opmedia-dev/k6_gpo_exhibit/firmware/src/phone_controller.h

#pragma once

#include <Arduino.h>
#include "config.h"
#include "phone_line.h"
#include "rotary_decoder.h"
#include "bell_driver.h"
#include "audio_player.h"
#include "control_panel.h"
#include "coin_box.h"

// ============================================================================
// Phone controller — exhibit state machine
//
// States:
//   IDLE             On-hook.  Auto-ring timer ticking.
//   RINGING          Bell ringing (auto or manual).  Awaiting pickup.
//   PLAYING_HISTORY  Handset answered a ring → playing a history track.
//   DIAL_TONE        Handset lifted without ring → dial tone plays.
//   DIALING          Digits accumulating from rotary dial.
//   AWAIT_COINS      (A+B only) Number recognised, waiting for coins.
//   AWAIT_BTN_A      (A+B only) Call connected, waiting for Button A.
//   AWAIT_BTN_B      (A+B only) Number not recognised, waiting for Button B.
//   RINGING_TONE    Outgoing call → playing UK ringing tone before connecting.
//   PLAYING_NUMBER   Dialling complete → matched MP3 playing.
//   PLAYING_NOT_REC  Dialling complete → "number not recognised" playing.
//   BUSY             Error / timeout → busy tone.
//   PLUGIN_SEQUENCE  Executing a JSON plugin script (multi-step).
// ============================================================================

enum class PhoneState : uint8_t {
    IDLE,
    RINGING,
    PLAYING_HISTORY,
    DIAL_TONE,
    DIALING,
    AWAIT_COINS,
    AWAIT_BTN_A,
    AWAIT_BTN_B,
    RINGING_TONE,
    PLAYING_NUMBER,
    PLAYING_NOT_REC,
    PLUGIN_SEQUENCE,
    BUSY
};

using DigitCallback   = void (*)(uint8_t digit);
using NumberCallback  = void (*)(const char* number);
using HookCallback    = void (*)(HookState state);
using StateCallback   = void (*)(PhoneState state);

class PhoneController {
public:
    void begin();
    void update();

    PhoneState state() const { return state_; }
    const char* stateName() const;

    void ring();
    void testRing(int seconds = 3);  // fixed-duration ring for bell testing
    void cancelRing();
    void hangUp();

    // Dial a number on the visitor's behalf, as if it had been dialled on the
    // rotary dial. The handset must be off the hook, just as it must be to dial
    // by hand. Returns false if the phone is not in a state to accept dialling
    // or the number contains no digits.
    bool dialRemote(const char* number);

    void onDigit(DigitCallback cb)   { digit_cb_  = cb; }
    void onNumber(NumberCallback cb) { number_cb_ = cb; }
    void onHook(HookCallback cb)     { hook_cb_   = cb; }
    void onState(StateCallback cb)   { state_cb_  = cb; }

    // Enable / disable the random auto-ring feature.
    void setAutoRing(bool enabled);
    bool autoRingEnabled() const   { return auto_ring_enabled_; }
    void toggleAutoRing()          { setAutoRing(!auto_ring_enabled_); }

    // Configurable auto-ring interval (milliseconds).
    void setAutoRingInterval(unsigned long minMs, unsigned long maxMs);
    unsigned long autoRingMinMs() const { return auto_ring_min_ms_; }
    unsigned long autoRingMaxMs() const { return auto_ring_max_ms_; }

    // Configurable max ring cadences (0 = unlimited).
    void setMaxRingCadences(int n) { max_ring_cadences_ = n; }
    int  maxRingCadences() const { return max_ring_cadences_; }

    // Configurable ringing tone duration range (seconds) for outgoing calls.
    void setRingToneRange(int minSecs, int maxSecs);
    int  ringToneMinSecs() const { return ring_tone_min_ms_ / 1000; }
    int  ringToneMaxSecs() const { return ring_tone_max_ms_ / 1000; }

    // Dial-pulse click: play a tick in the earpiece on each rotary pulse.
    void setDialTicks(bool on) { dial_ticks_ = on; }
    bool dialTicks() const     { return dial_ticks_; }

    // Inter-digit gap: how long the system waits after the last dialled digit
    // before deciding the number is complete. Longer values give slower or
    // less-experienced visitors more time between digits on the rotary dial.
    void setNumberCompleteMs(unsigned long ms) { number_complete_ms_ = ms; }
    unsigned long numberCompleteMs() const     { return number_complete_ms_; }

    // Usage alert: lamp flashes if no activity for this many minutes (0=disabled).
    void setAlertIdleMinutes(int mins) { alert_idle_ms_ = mins * 60000UL; }
    int  alertIdleMinutes() const { return alert_idle_ms_ / 60000; }
    bool isAlertActive() const;

    // Plugin system.
    bool tryPlugin(const char* number);

    PhoneLine&      line()    { return line_; }
    BellDriver&     bell()    { return bell_; }
    AudioPlayer&    player()  { return player_; }
    RotaryDecoder&  dial()    { return dial_; }
    ControlPanel&   panel()   { return panel_; }
    CoinBox&        coinBox() { return coin_box_; }

    const char* dialledNumber() const { return dialled_; }
    unsigned long stateEnterTime() const { return state_enter_time_; }

private:
    void enterState(PhoneState s);
    void resetAutoRingTimer();
    void updateLamp();

    PhoneState     state_ = PhoneState::IDLE;
    PhoneLine      line_;
    RotaryDecoder  dial_;
    BellDriver     bell_;
    AudioPlayer    player_;
    ControlPanel   panel_;
    CoinBox        coin_box_;

    char           dialled_[MAX_DIALLED_DIGITS + 1] = {};
    char           pending_path_[64] = {};  // path to play after coins inserted
    uint8_t        dial_pos_ = 0;

    unsigned long  state_enter_time_ = 0;
    unsigned long  test_ring_end_    = 0;  // fixed-duration test ring end (0=off)
    unsigned long  last_digit_time_  = 0;
    bool           replace_prompted_ = false;  // "replace handset" already played
    bool           dial_ticks_       = false;  // click earpiece on each dial pulse
    unsigned long  number_complete_ms_ = NUMBER_COMPLETE_MS;  // inter-digit gap

    // Auto-ring
    bool           auto_ring_enabled_ = true;
    unsigned long  next_ring_time_    = 0;
    unsigned long  auto_ring_min_ms_  = AUTO_RING_MIN_MS;
    unsigned long  auto_ring_max_ms_  = AUTO_RING_MAX_MS;
    int            max_ring_cadences_ = DEFAULT_MAX_RING_CADENCES;
    int            ring_cadence_count_ = 0;
    unsigned long  ring_tone_min_ms_ = DEFAULT_RING_TONE_MS;
    unsigned long  ring_tone_max_ms_ = DEFAULT_RING_TONE_MS;
    unsigned long  ring_tone_target_ = DEFAULT_RING_TONE_MS;  // randomised per call

    // Usage alert
    unsigned long  last_activity_ms_  = 0;   // last hook/call activity
    unsigned long  alert_idle_ms_     = 7200000;  // 2 hours default

    // Plugin sequencer
    static const int MAX_PLUGIN_STEPS = 10;
    struct PluginStep { char action; char path[48]; unsigned long ms; };
    PluginStep     plugin_steps_[MAX_PLUGIN_STEPS];
    int            plugin_count_     = 0;
    int            plugin_index_     = 0;
    unsigned long  plugin_step_time_ = 0;

    DigitCallback  digit_cb_  = nullptr;
    NumberCallback number_cb_ = nullptr;
    HookCallback   hook_cb_   = nullptr;
    StateCallback  state_cb_  = nullptr;
};
